LurCotte/Smart-Home-Electronic-Safety-and-Monitoring-System/Progress/Week 1/Deskripsi Proyek.png

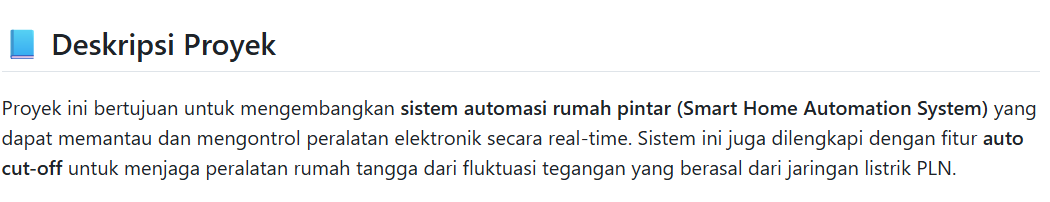
Progress/Week 1/Deskripsi Proyek.png
