LurCotte/Smart-Home-Electronic-Safety-and-Monitoring-System/Progress/Week 1/Fitur Utama.png

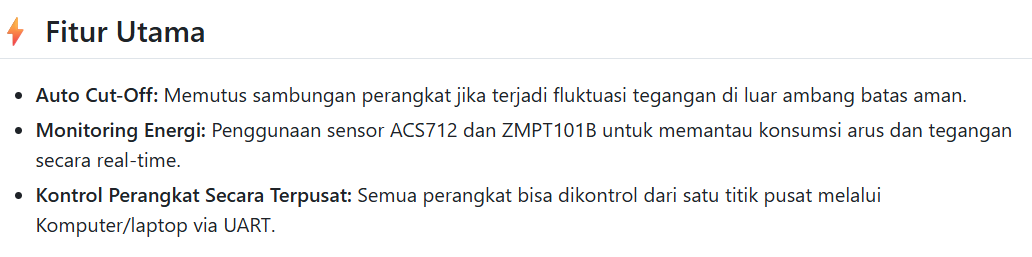
Progress/Week 1/Fitur Utama.png
