LurCotte/Smart-Home-Electronic-Safety-and-Monitoring-System/Progress/Week 1/Fungsi Komponen.png

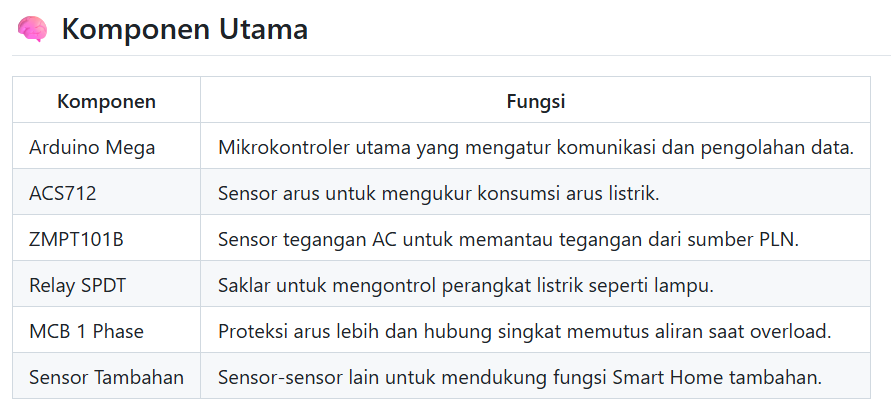
Progress/Week 1/Fungsi Komponen.png
