LurCotte/Smart-Home-Electronic-Safety-and-Monitoring-System/Progress/Week 1/Penjelasan Alur Sistem.png

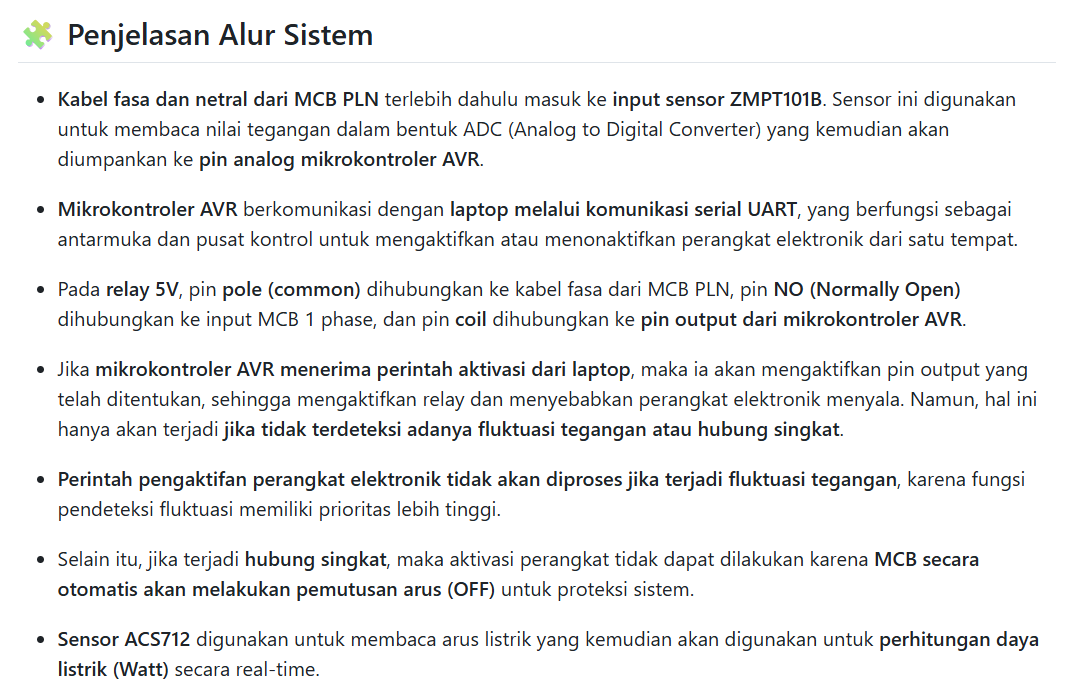
Progress/Week 1/Penjelasan Alur Sistem.png
