LurCotte/Smart-Home-Electronic-Safety-and-Monitoring-System/Progress/Week 3/mendeteksi tegangan rms.jpeg

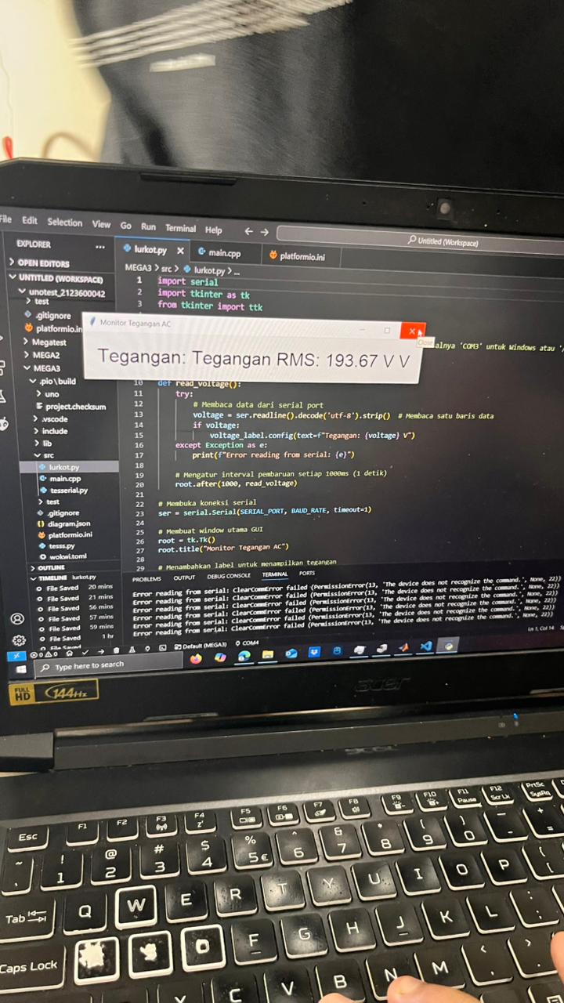
Progress/Week 3/mendeteksi tegangan rms.jpeg
