LurCotte/Smart-Home-Electronic-Safety-and-Monitoring-System/Progress/Week 3/Profile.png

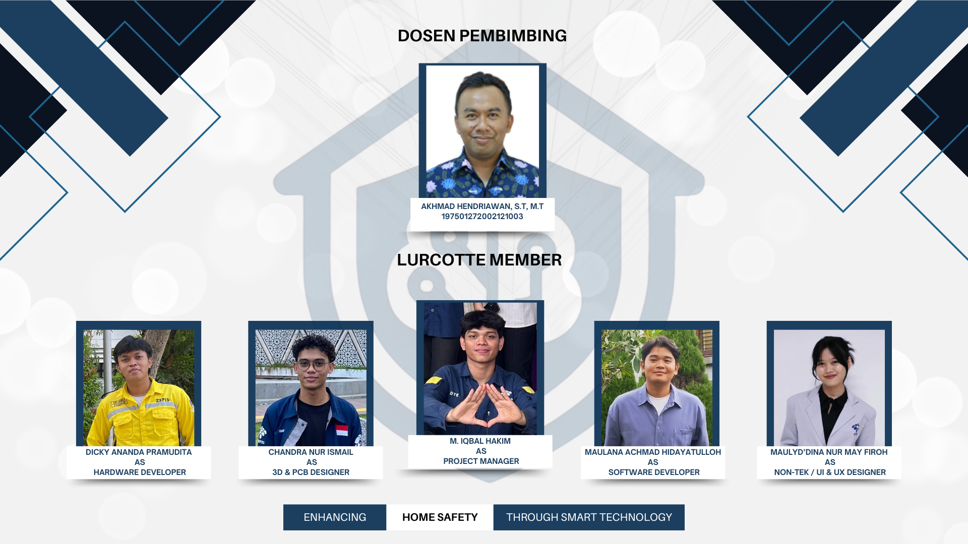
Progress/Week 3/Profile.png
