LurCotte/Smart-Home-Electronic-Safety-and-Monitoring-System/Progress/Week 5/Hasil akhir.jpg

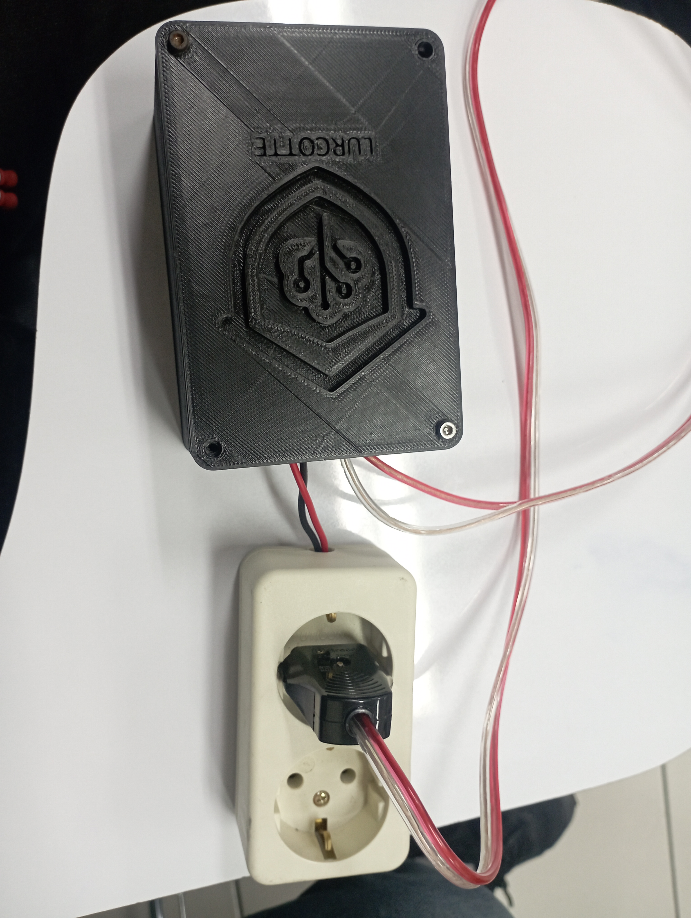
Progress/Week 5/Hasil akhir.jpg
